shreaypatel/macroPad/CAD/mpAngle1.png

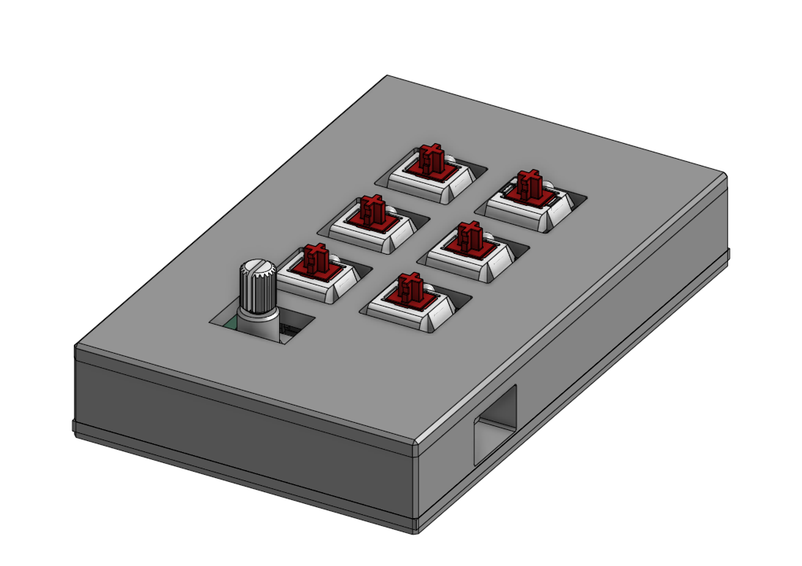
CAD/mpAngle1.png
