shreaypatel/macroPad/CAD/mpAngle3.png

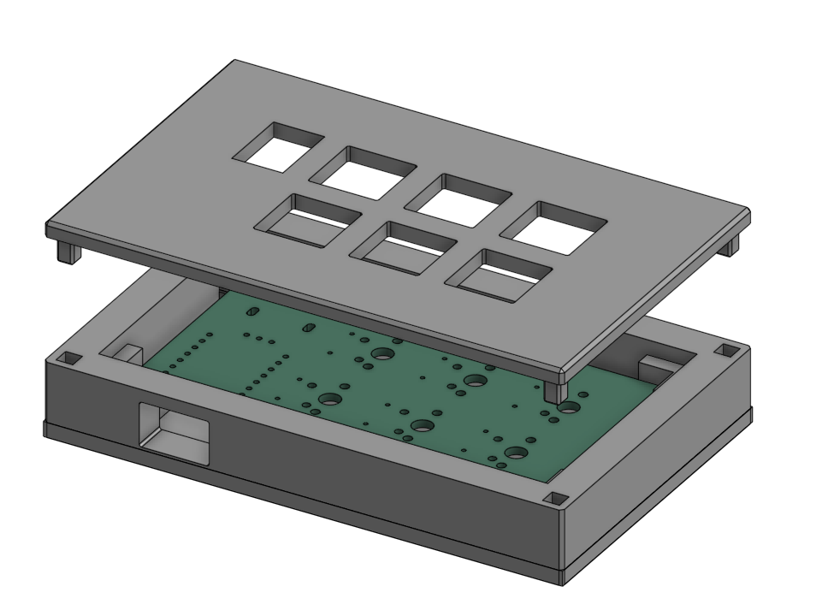
CAD/mpAngle3.png
