shreaypatel/macroPad/PCB/pcb3dAngle_2.png

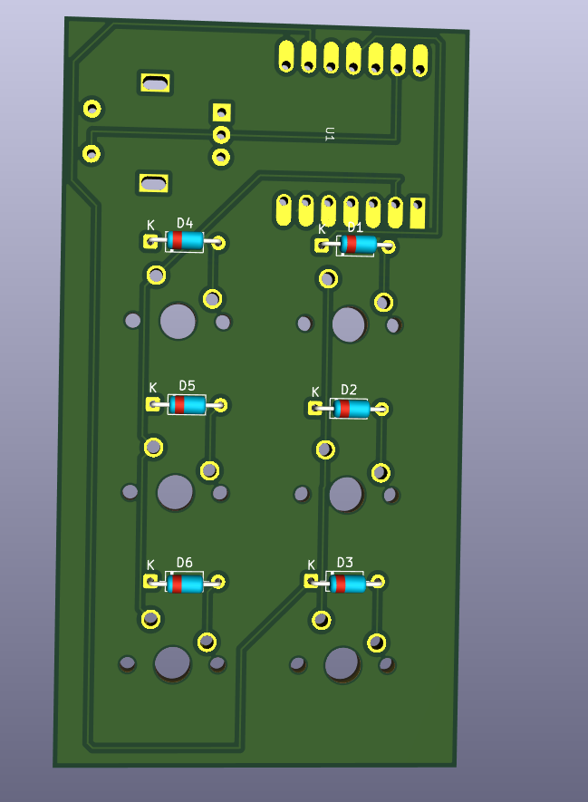
PCB/pcb3dAngle_2.png
